DergLabs/SPI2TTL/Hardware/SPI2TTL/FPGA.kicad_sch

## KiCad design Hardware/SPI2TTL/FPGA.kicad_sch (2024-07-24)

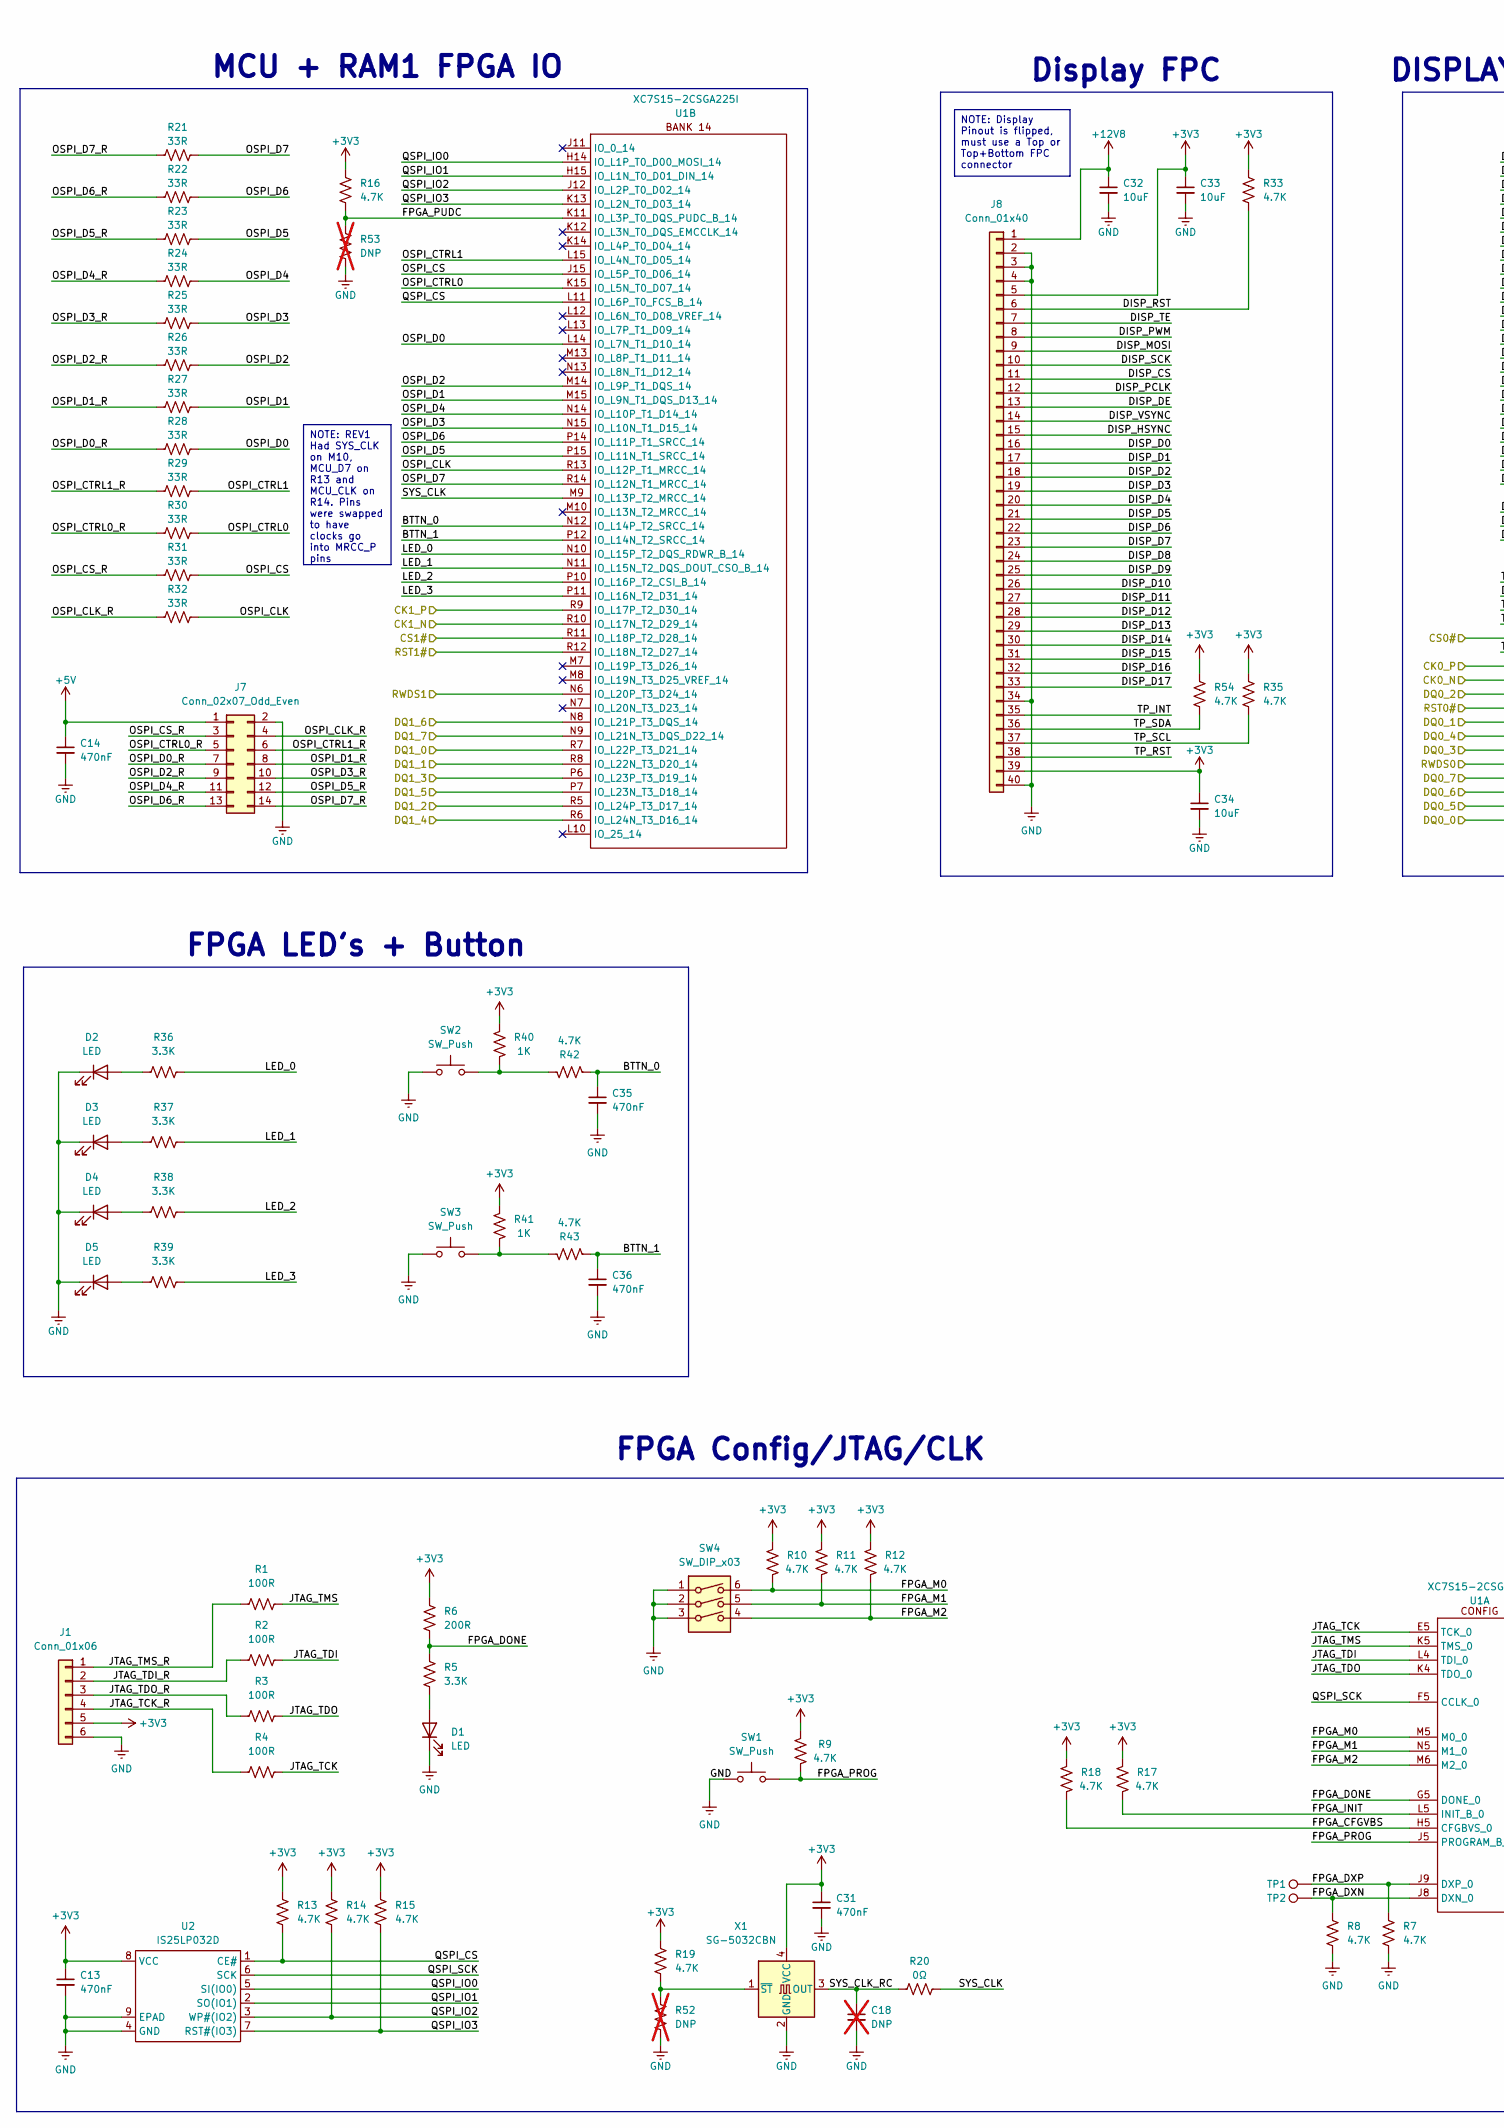
[picture p2: schematic FPGA.kicad_sch, part in row 1, column 1]

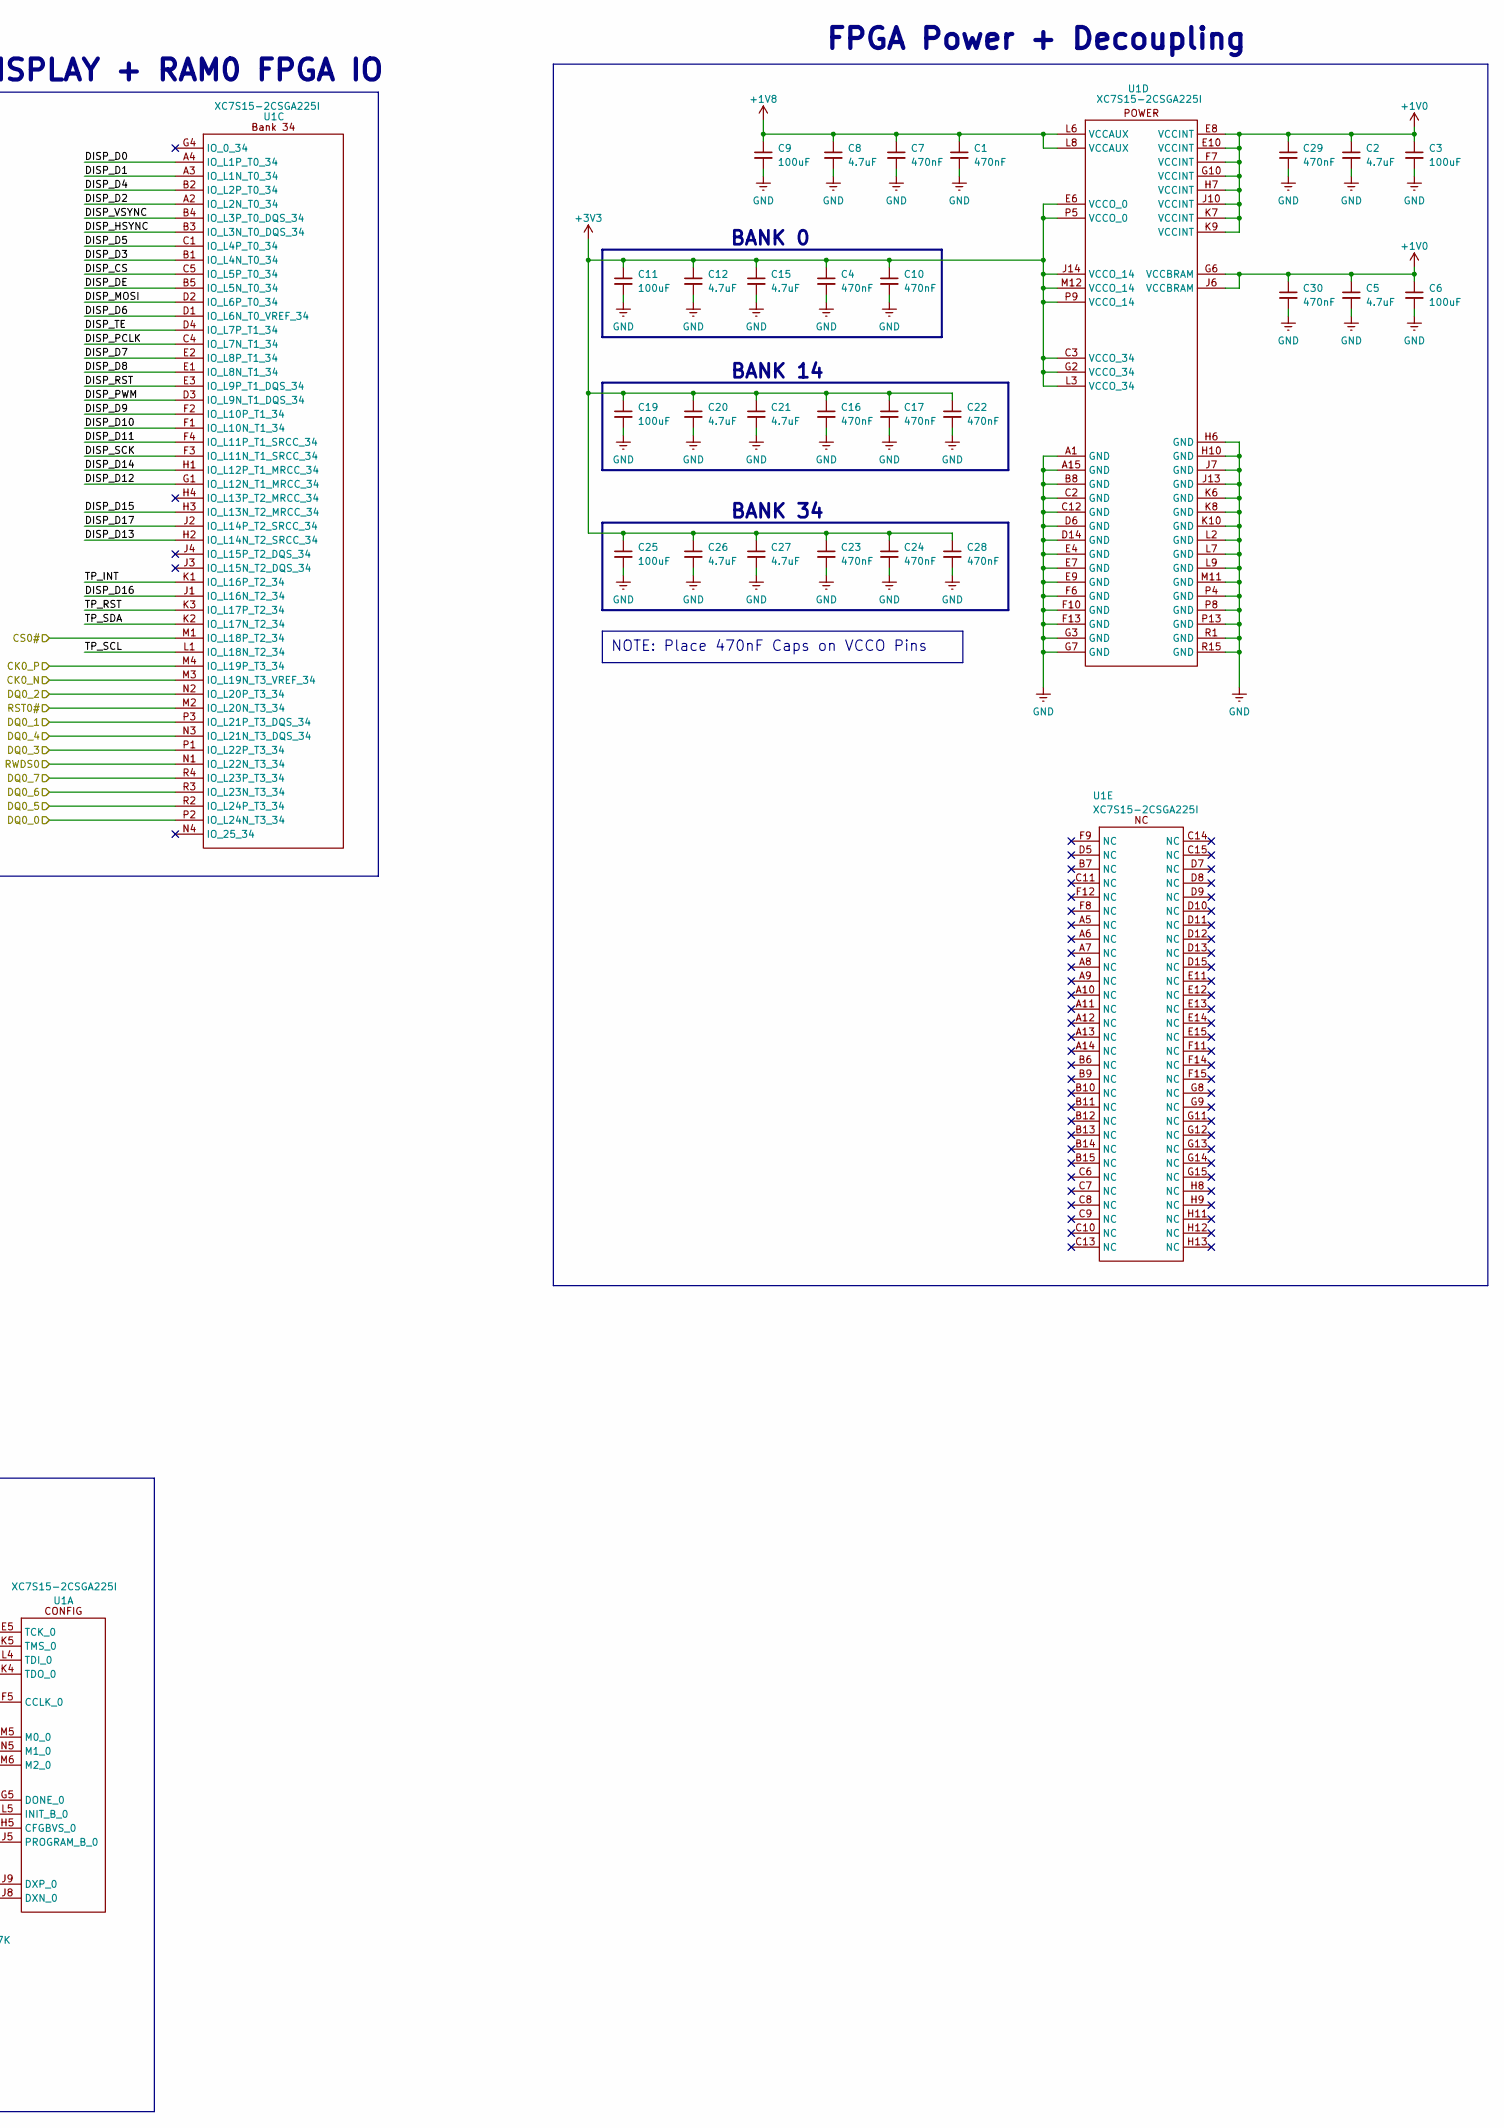
[picture p3: schematic FPGA.kicad_sch, part in row 1, column 2]

Parts:
C1, C4, C7, C10, C16, C17, C22, C23, C24, C28, C29, C30: 470nF; C_0201_0603Metric
C2, C5, C8, C12, C15, C20, C21, C26, C27: 4.7uF; C_0201_0603Metric
C3, C6, C9, C11, C19, C25: 100uF; C_0805_2012Metric
C13, C14, C31, C35, C36: 470nF; C_0402_1005Metric
C18: DNP; C_0402_1005Metric; not fitted
C32, C33, C34: 10uF; C_0603_1608Metric
D1, D2, D3, D4, D5: LED; LED_0603_1608Metric
J1: Conn_01x06; PinHeader_1x06_P2.54mm_Vertical
J7: Conn_02x07_Odd_Even; PinHeader_2x07_P2.54mm_Horizontal
J8: Conn_01x40; Hirose_FH12-40S-0.5SH_1x40-1MP_P0.50mm_Horizontal
R1, R2, R3, R4: 100R; R_0402_1005Metric
R5, R36, R37, R38, R39: 3.3K; R_0402_1005Metric
R6: 200R; R_0402_1005Metric
R7, R8, R9, R10, R11, R12, R13, R14, R15, R16, R17, R18, R19, R33, R35, R42, R43, R54: 4.7K; R_0402_1005Metric
R20: 0Ω; R_0402_1005Metric
R21, R22, R23, R24, R25, R26, R27, R28, R29, R30, R31, R32: 33R; R_0402_1005Metric
R40, R41: 1K; R_0402_1005Metric
R52, R53: DNP; R_0402_1005Metric; not fitted
SW1, SW2, SW3: SW_Push; SW_SPST_PTS645
SW4: SW_DIP_x03; SW_DIP_SPSTx03_Slide_KingTek_DSHP03TJ_W5.25mm_P1.27mm_JPin; MPN 416131160803
TP1, TP2: TestPoint; TestPoint_Pad_D1.0mm
U1: XC7S15-2CSGA225I; CSGA225_XIL
U2: IS25LP032D; WSON-8-1EP_6x5mm_P1.27mm_EP3.4x4mm
X1: SG-5032CBN; Oscillator_SMD_SeikoEpson_SG8002LB-4Pin_5.0x3.2mm

Connections:
+1V0: C2.1, C3.1, C5.1, C6.1, C29.1, C30.1, U1.E8 (VCCINT), U1.E10 (VCCINT), U1.F7 (VCCINT), U1.G6 (VCCBRAM), U1.G10 (VCCINT), U1.H7 (VCCINT), U1.J6 (VCCBRAM), U1.J10 (VCCINT), U1.K7 (VCCINT), U1.K9 (VCCINT)
+1V8: C1.1, C7.1, C8.1, C9.1, U1.L6 (VCCAUX), U1.L8 (VCCAUX)
+3V3: C4.1, C10.1, C11.1, C12.1, C13.1, C15.1, C16.1, C17.1, C19.1, C20.1, C21.1, C22.1, C23.1, C24.1, C25.1, C26.1, C27.1, C28.1, C31.1, C33.1, C34.1, J1.5, J8.5, J8.39, R6.2, R9.2, R10.2, R11.2, R12.2, R13.2, R14.2, R15.2, R16.2, R17.2, R18.2, R19.2, R33.2, R35.2, R40.2, R41.2, R54.2, U1.C3 (VCCO_34), U1.E6 (VCCO_0), U1.G2 (VCCO_34), U1.J14 (VCCO_14), U1.L3 (VCCO_34), U1.M12 (VCCO_14), U1.P5 (VCCO_0), U1.P9 (VCCO_14), U2.8 (VCC), X1.4 (VCC)
+5V: C14.1, J7.1
+12V8: C32.1, J8.1
BTTN_0: C35.1, R42.1, U1.N12 (IO_L14P_T2_SRCC_14)
BTTN_1: C36.1, R43.1, U1.P12 (IO_L14N_T2_SRCC_14)
CK0_N: U1.M3 (IO_L19N_T3_VREF_34)
CK0_P: U1.M4 (IO_L19P_T3_34)
CK1_N: U1.R10 (IO_L17N_T2_D29_14)
CK1_P: U1.R9 (IO_L17P_T2_D30_14)
CS0#: U1.M1 (IO_L18P_T2_34)
CS1#: U1.R11 (IO_L18P_T2_D28_14)
DISP_CS: J8.11, U1.C5 (IO_L5P_T0_34)
DISP_D0: J8.16, U1.A4 (IO_L1P_T0_34)
DISP_D1: J8.17, U1.A3 (IO_L1N_T0_34)
DISP_D2: J8.18, U1.A2 (IO_L2N_T0_34)
DISP_D3: J8.19, U1.B1 (IO_L4N_T0_34)
DISP_D4: J8.20, U1.B2 (IO_L2P_T0_34)
DISP_D5: J8.21, U1.C1 (IO_L4P_T0_34)
DISP_D6: J8.22, U1.D1 (IO_L6N_T0_VREF_34)
DISP_D7: J8.23, U1.E2 (IO_L8P_T1_34)
DISP_D8: J8.24, U1.E1 (IO_L8N_T1_34)
DISP_D9: J8.25, U1.F2 (IO_L10P_T1_34)
DISP_D10: J8.26, U1.F1 (IO_L10N_T1_34)
DISP_D11: J8.27, U1.F4 (IO_L11P_T1_SRCC_34)
DISP_D12: J8.28, U1.G1 (IO_L12N_T1_MRCC_34)
DISP_D13: J8.29, U1.H2 (IO_L14N_T2_SRCC_34)
DISP_D14: J8.30, U1.H1 (IO_L12P_T1_MRCC_34)
DISP_D15: J8.31, U1.H3 (IO_L13N_T2_MRCC_34)
DISP_D16: J8.32, U1.J1 (IO_L16N_T2_34)
DISP_D17: J8.33, U1.J2 (IO_L14P_T2_SRCC_34)
DISP_DE: J8.13, U1.B5 (IO_L5N_T0_34)
DISP_HSYNC: J8.15, U1.B3 (IO_L3N_T0_DQS_34)
DISP_MOSI: J8.9, U1.D2 (IO_L6P_T0_34)
DISP_PCLK: J8.12, U1.C4 (IO_L7N_T1_34)
DISP_PWM: J8.8, U1.D3 (IO_L9N_T1_DQS_34)
DISP_RST: J8.6, R33.1, U1.E3 (IO_L9P_T1_DQS_34)
DISP_SCK: J8.10, U1.F3 (IO_L11N_T1_SRCC_34)
DISP_TE: J8.7, U1.D4 (IO_L7P_T1_34)
DISP_VSYNC: J8.14, U1.B4 (IO_L3P_T0_DQS_34)
DQ0_0: U1.P2 (IO_L24N_T3_34)
DQ0_1: U1.P3 (IO_L21P_T3_DQS_34)
DQ0_2: U1.N2 (IO_L20P_T3_34)
DQ0_3: U1.P1 (IO_L22P_T3_34)
DQ0_4: U1.N3 (IO_L21N_T3_DQS_34)
DQ0_5: U1.R2 (IO_L24P_T3_34)
DQ0_6: U1.R3 (IO_L23N_T3_34)
DQ0_7: U1.R4 (IO_L23P_T3_34)
DQ1_0: U1.R7 (IO_L22P_T3_D21_14)
DQ1_1: U1.R8 (IO_L22N_T3_D20_14)
DQ1_2: U1.R5 (IO_L24P_T3_D17_14)
DQ1_3: U1.P6 (IO_L23P_T3_D19_14)
DQ1_4: U1.R6 (IO_L24N_T3_D16_14)
DQ1_5: U1.P7 (IO_L23N_T3_D18_14)
DQ1_6: U1.N8 (IO_L21P_T3_DQS_14)
DQ1_7: U1.N9 (IO_L21N_T3_DQS_D22_14)
FPGA_CFGVBS: R18.1, U1.H5 (CFGBVS_0)
FPGA_DONE: R5.2, R6.1, U1.G5 (DONE_0)
FPGA_DXN: R8.2, TP2.1, U1.J8 (DXN_0)
FPGA_DXP: R7.2, TP1.1, U1.J9 (DXP_0)
FPGA_INIT: R17.1, U1.L5 (INIT_B_0)
FPGA_M0: R10.1, SW4.6, U1.M5 (M0_0)
FPGA_M1: R11.1, SW4.5, U1.N5 (M1_0)
FPGA_M2: R12.1, SW4.4, U1.M6 (M2_0)
FPGA_PROG: R9.1, SW1.1, U1.J5 (PROGRAM_B_0)
FPGA_PUDC: R16.1, R53.2, U1.K11 (IO_L3P_T0_DQS_PUDC_B_14)
GND: C1.2, C2.2, C3.2, C4.2, C5.2, C6.2, C7.2, C8.2, C9.2, C10.2, C11.2, C12.2, C13.2, C14.2, C15.2, C16.2, C17.2, C18.2, C19.2, C20.2, C21.2, C22.2, C23.2, C24.2, C25.2, C26.2, C27.2, C28.2, C29.2, C30.2, C31.2, C32.2, C33.2, C34.2, C35.2, C36.2, D1.1 (K), D2.1 (K), D3.1 (K), D4.1 (K), D5.1 (K), J1.6, J7.2, J8.2, J8.3, J8.4, J8.34, J8.40, R7.1, R8.1, R52.1, R53.1, SW1.2, SW2.2, SW3.2, SW4.1, SW4.2, SW4.3, U1.A1 (GND), U1.A15 (GND), U1.B8 (GND), U1.C2 (GND), U1.C12 (GND), U1.D6 (GND), U1.D14 (GND), U1.E4 (GND), U1.E7 (GND), U1.E9 (GND), U1.F6 (GND), U1.F10 (GND), U1.F13 (GND), U1.G3 (GND), U1.G7 (GND), U1.H6 (GND), U1.H10 (GND), U1.J7 (GND), U1.J13 (GND), U1.K6 (GND), U1.K8 (GND), U1.K10 (GND), U1.L2 (GND), U1.L7 (GND), U1.L9 (GND), U1.M11 (GND), U1.P4 (GND), U1.P8 (GND), U1.P13 (GND), U1.R1 (GND), U1.R15 (GND), U2.4 (GND), U2.9 (EPAD), X1.2 (GND)
JTAG_TCK: R4.2, U1.E5 (TCK_0)
JTAG_TCK_R: J1.4, R4.1
JTAG_TDI: R2.2, U1.L4 (TDI_0)
JTAG_TDI_R: J1.2, R2.1
JTAG_TDO: R3.2, U1.K4 (TDO_0)
JTAG_TDO_R: J1.3, R3.1
JTAG_TMS: R1.2, U1.K5 (TMS_0)
JTAG_TMS_R: J1.1, R1.1
LED_0: R36.1, U1.N10 (IO_L15P_T2_DQS_RDWR_B_14)
LED_1: R37.1, U1.N11 (IO_L15N_T2_DQS_DOUT_CSO_B_14)
LED_2: R38.1, U1.P10 (IO_L16P_T2_CSI_B_14)
LED_3: R39.1, U1.P11 (IO_L16N_T2_D31_14)
unnamed: D1.2 (A), R5.1
unnamed: D2.2 (A), R36.2
unnamed: D3.2 (A), R37.2
unnamed: D4.2 (A), R38.2
unnamed: D5.2 (A), R39.2
unnamed: R19.1, R52.2, X1.1 (~ST)
unnamed: R40.1, R42.2, SW2.1
unnamed: R41.1, R43.2, SW3.1
OSPI_CLK: R32.2, U1.R13 (IO_L12P_T1_MRCC_14)
OSPI_CLK_R: J7.4, R32.1
OSPI_CS: R31.2, U1.J15 (IO_L5P_T0_D06_14)
OSPI_CS_R: J7.3, R31.1
OSPI_CTRL0: R30.2, U1.K15 (IO_L5N_T0_D07_14)
OSPI_CTRL0_R: J7.5, R30.1
OSPI_CTRL1: R29.2, U1.L15 (IO_L4N_T0_D05_14)
OSPI_CTRL1_R: J7.6, R29.1
OSPI_D0: R28.2, U1.L14 (IO_L7N_T1_D10_14)
OSPI_D0_R: J7.7, R28.1
OSPI_D1: R27.2, U1.M15 (IO_L9N_T1_DQS_D13_14)
OSPI_D1_R: J7.8, R27.1
OSPI_D2: R26.2, U1.M14 (IO_L9P_T1_DQS_14)
OSPI_D2_R: J7.9, R26.1
OSPI_D3: R25.2, U1.N15 (IO_L10N_T1_D15_14)
OSPI_D3_R: J7.10, R25.1
OSPI_D4: R24.2, U1.N14 (IO_L10P_T1_D14_14)
OSPI_D4_R: J7.11, R24.1
OSPI_D5: R23.2, U1.P15 (IO_L11N_T1_SRCC_14)
OSPI_D5_R: J7.12, R23.1
OSPI_D6: R22.2, U1.P14 (IO_L11P_T1_SRCC_14)
OSPI_D6_R: J7.13, R22.1
OSPI_D7: R21.2, U1.R14 (IO_L12N_T1_MRCC_14)
OSPI_D7_R: J7.14, R21.1
QSPI_CS: R13.1, U1.L11 (IO_L6P_T0_FCS_B_14), U2.1 (CE#)
QSPI_IO0: U1.H14 (IO_L1P_T0_D00_MOSI_14), U2.5 (SI(IO0))
QSPI_IO1: U1.H15 (IO_L1N_T0_D01_DIN_14), U2.2 (SO(IO1))
QSPI_IO2: R14.1, U1.J12 (IO_L2P_T0_D02_14), U2.3 (WP#(IO2))
QSPI_IO3: R15.1, U1.K13 (IO_L2N_T0_D03_14), U2.7 (RST#(IO3))
QSPI_SCK: U1.F5 (CCLK_0), U2.6 (SCK)
RST0#: U1.M2 (IO_L20N_T3_34)
RST1#: U1.R12 (IO_L18N_T2_D27_14)
RWDS0: U1.N1 (IO_L22N_T3_34)
RWDS1: U1.N6 (IO_L20P_T3_D24_14)
SYS_CLK: R20.2, U1.M9 (IO_L13P_T2_MRCC_14)
SYS_CLK_RC: C18.1, R20.1, X1.3 (OUT)
TP_INT: J8.35, U1.K1 (IO_L16P_T2_34)
TP_RST: J8.38, U1.K3 (IO_L17P_T2_34)
TP_SCL: J8.37, R35.1, U1.L1 (IO_L18N_T2_34)
TP_SDA: J8.36, R54.1, U1.K2 (IO_L17N_T2_34)

Notes on the sheet:
NOTE: REV1 Had SYS_CLK on M10, MCU_D7 on R13 and MCU_CLK on R14. Pins were swapped to have clocks go into MRCC_P pins
NOTE: Display Pinout is flipped, must use a Top or Top+Bottom FPC connector
NOTE: Place 470nF Caps on VCCO Pins
FPGA Config/JTAG/CLK
Display FPC
FPGA Power + Decoupling
FPGA LED's + Button
MCU + RAM1 FPGA IO
BANK 0
BANK 34
BANK 14
DISPLAY + RAM0 FPGA IO
