DergLabs/SPI2TTL/Hardware/SPI2TTL/Frame Memory.kicad_sch

## KiCad design Hardware/SPI2TTL/Frame Memory.kicad_sch (2024-07-21)

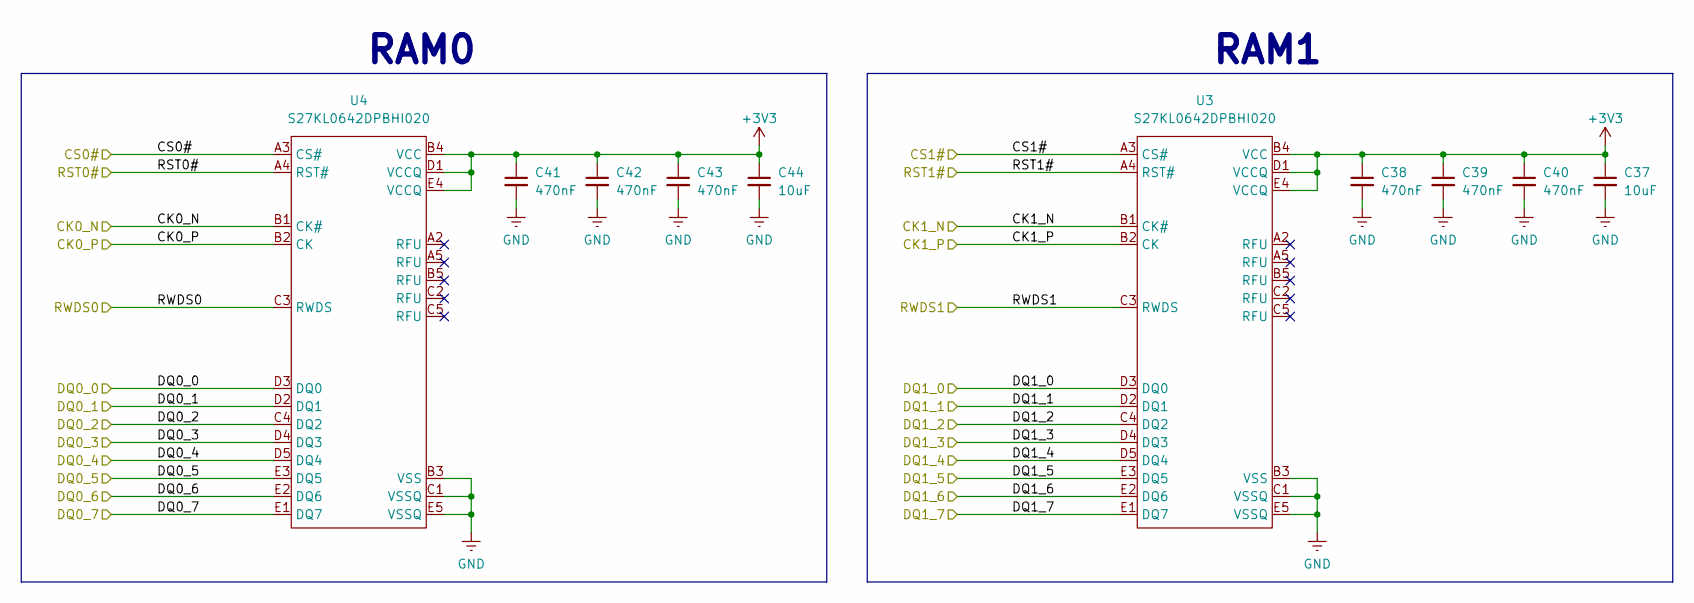
[picture p4: schematic Frame Memory.kicad_sch]

Parts:
C37, C44: 10uF; C_0603_1608Metric
C38, C39, C40, C41, C42, C43: 470nF; C_0402_1005Metric
U3, U4: S27KL0642DPBHI020; BGA-25-6x8mm

Connections:
+3V3: C37.1, C38.1, C39.1, C40.1, C41.1, C42.1, C43.1, C44.1, U3.B4 (VCC), U3.D1 (VCCQ), U3.E4 (VCCQ), U4.B4 (VCC), U4.D1 (VCCQ), U4.E4 (VCCQ)
CK0_N: U4.B1 (CK#)
CK0_P: U4.B2 (CK)
CK1_N: U3.B1 (CK#)
CK1_P: U3.B2 (CK)
CS0#: U4.A3 (CS#)
CS1#: U3.A3 (CS#)
DQ0_0: U4.D3 (DQ0)
DQ0_1: U4.D2 (DQ1)
DQ0_2: U4.C4 (DQ2)
DQ0_3: U4.D4 (DQ3)
DQ0_4: U4.D5 (DQ4)
DQ0_5: U4.E3 (DQ5)
DQ0_6: U4.E2 (DQ6)
DQ0_7: U4.E1 (DQ7)
DQ1_0: U3.D3 (DQ0)
DQ1_1: U3.D2 (DQ1)
DQ1_2: U3.C4 (DQ2)
DQ1_3: U3.D4 (DQ3)
DQ1_4: U3.D5 (DQ4)
DQ1_5: U3.E3 (DQ5)
DQ1_6: U3.E2 (DQ6)
DQ1_7: U3.E1 (DQ7)
GND: C37.2, C38.2, C39.2, C40.2, C41.2, C42.2, C43.2, C44.2, U3.B3 (VSS), U3.C1 (VSSQ), U3.E5 (VSSQ), U4.B3 (VSS), U4.C1 (VSSQ), U4.E5 (VSSQ)
RST0#: U4.A4 (RST#)
RST1#: U3.A4 (RST#)
RWDS0: U4.C3 (RWDS)
RWDS1: U3.C3 (RWDS)

Notes on the sheet:
RAM1
RAM0
