DergLabs/SPI2TTL/Hardware/SPI2TTL/Power.kicad_sch

## KiCad design Hardware/SPI2TTL/Power.kicad_sch (2024-07-24)

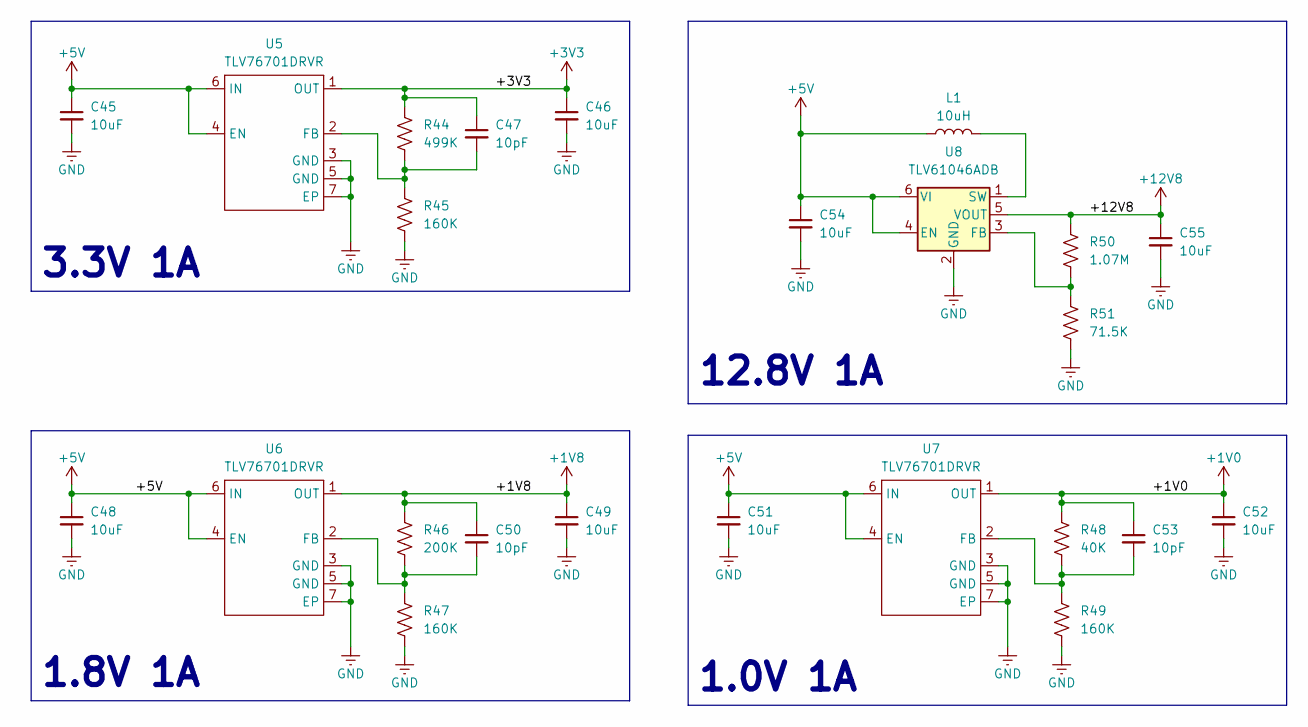
[picture p5: schematic Power.kicad_sch]

Parts:
C45, C46, C48, C49, C51, C52, C54, C55: 10uF; C_0603_1608Metric
C47, C50, C53: 10pF; C_0402_1005Metric
L1: 10uH; L_Wuerth_MAPI-3010; MPN 744025100
R44: 499K; R_0402_1005Metric
R45, R47, R49: 160K; R_0402_1005Metric
R46: 200K; R_0402_1005Metric
R48: 40K; R_0402_1005Metric
R50: 1.07M; R_0402_1005Metric
R51: 71.5K; R_0402_1005Metric
U5, U6, U7: TLV76701DRVR; WSON-6-1EP_2x2mm_P0.65mm_EP1x1.6mm
U8: TLV61046ADB; SOT-23-6

Connections:
+1V0: C52.1, C53.1, R48.2, U7.1 (OUT)
+1V8: C49.1, C50.1, R46.2, U6.1 (OUT)
+3V3: C46.1, C47.1, R44.2, U5.1 (OUT)
+5V: C45.1, C48.1, C51.1, C54.1, L1.1, U5.4 (EN), U5.6 (IN), U6.4 (EN), U6.6 (IN), U7.4 (EN), U7.6 (IN), U8.4 (EN), U8.6 (VI)
+12V8: C55.1, R50.2, U8.5 (VOUT)
GND: C45.2, C46.2, C48.2, C49.2, C51.2, C52.2, C54.2, C55.2, R45.1, R47.1, R49.1, R51.1, U5.3 (GND), U5.5 (GND), U5.7 (EP), U6.3 (GND), U6.5 (GND), U6.7 (EP), U7.3 (GND), U7.5 (GND), U7.7 (EP), U8.2 (GND)
unnamed: C47.2, R44.1, R45.2, U5.2 (FB)
unnamed: C50.2, R46.1, R47.2, U6.2 (FB)
unnamed: C53.2, R48.1, R49.2, U7.2 (FB)
unnamed: L1.2, U8.1 (SW)
unnamed: R50.1, R51.2, U8.3 (FB)

Notes on the sheet:
3.3V 1A
12.8V 1A
1.8V 1A
1.0V 1A
