DergLabs/SPI2TTL/Hardware/SPI2TTL/SPI2TTL.kicad_sch

## KiCad design Hardware/SPI2TTL/SPI2TTL.kicad_sch (2024-07-21)

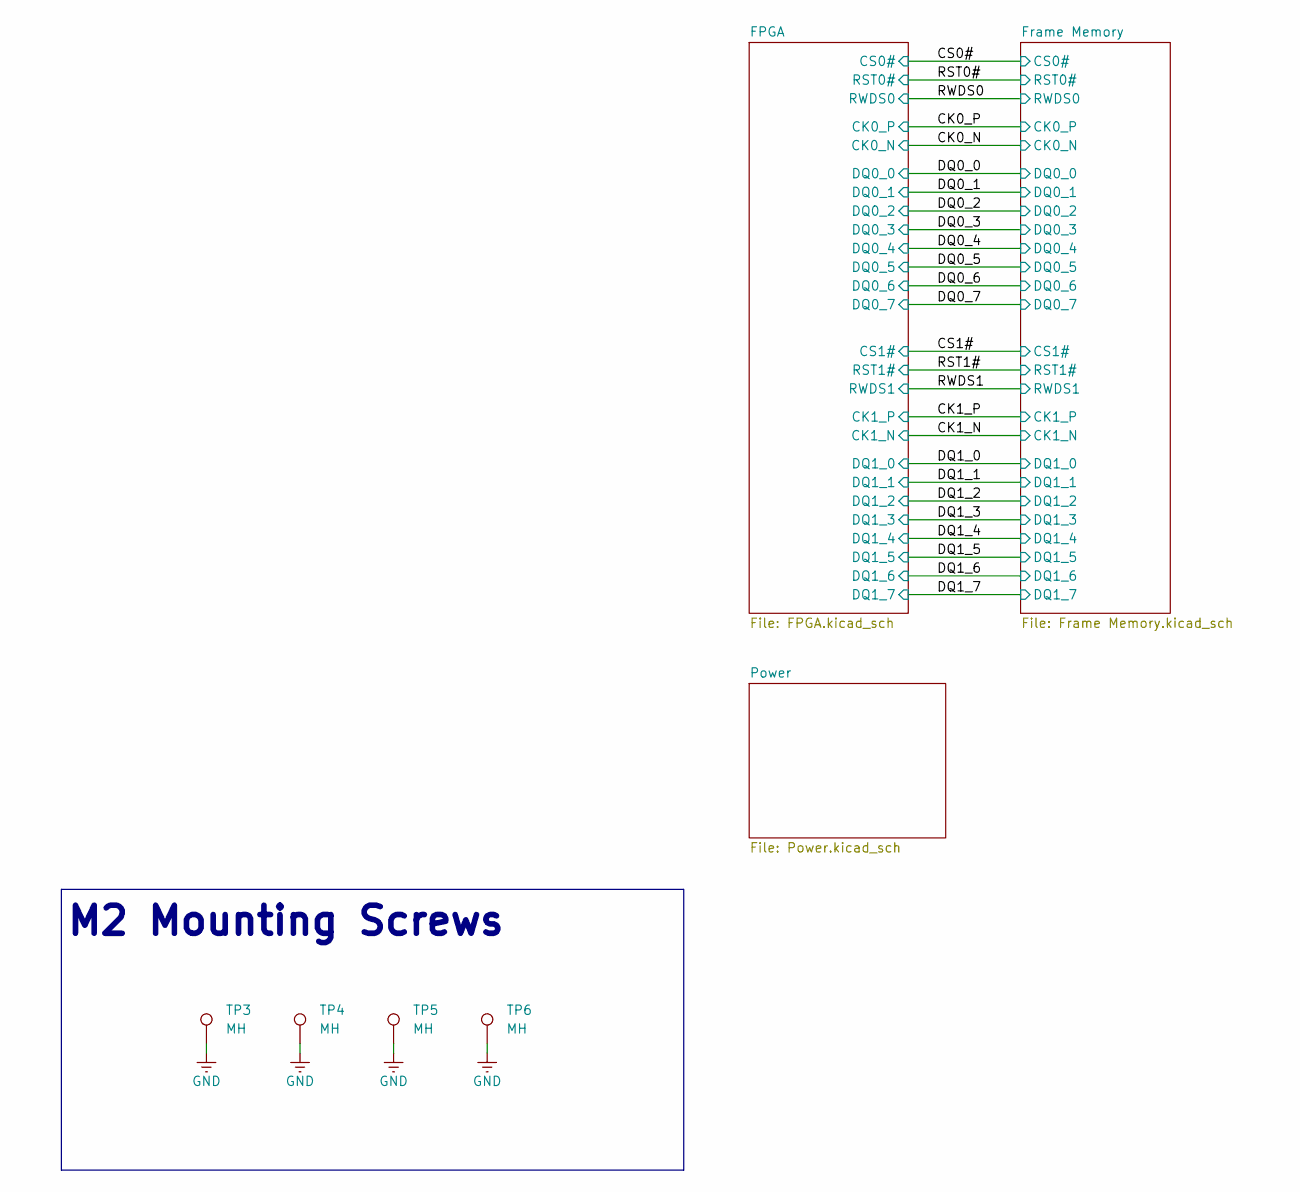
[picture p6: schematic SPI2TTL.kicad_sch]

Parts:
TP3, TP4, TP5, TP6: MH; MountingHole_2.2mm_M2_Pad_Via

Connections:
GND: TP3.1, TP4.1, TP5.1, TP6.1

Notes on the sheet:
M2 Mounting Screws
